tpII/2024-J2-CameraTracker/Diseños 3D/STLs/v7/base v21.stl

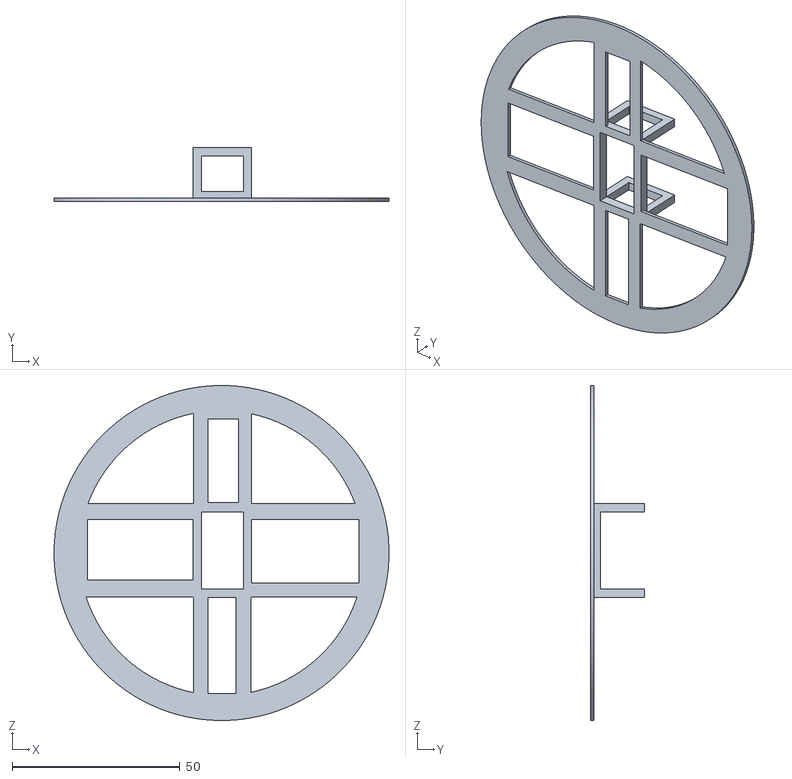
[picture p21: CAD file, 2024-12-09, an earlier design]
Diseños 3D/STLs/v7/base v21.stl
100.0 x 16.0 x 100.0
