tpII/2024-J2-CameraTracker/Diseños 3D/STLs/v2/Servo 2 v16.stl

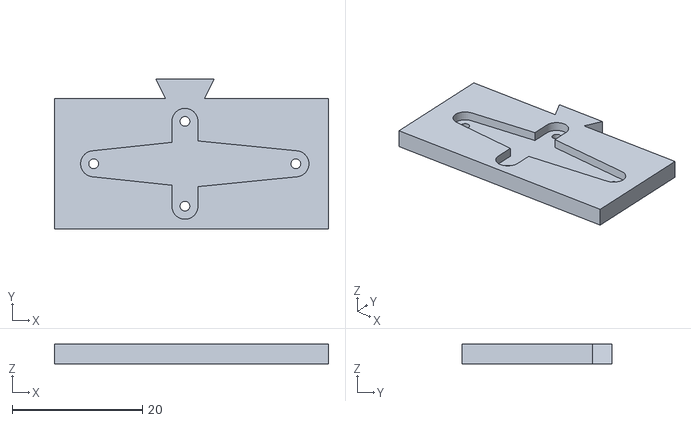
[picture p22: CAD file, 2024-10-07, an earlier design]
Diseños 3D/STLs/v2/Servo 2 v16.stl
42.0 x 23.0 x 3.00
