tpII/2024-J2-CameraTracker/CameraWebServer/web_server.h

#include <WiFi.h>
#include "esp_timer.h"
#include "img_converters.h"
#include "Arduino.h"
#include "fb_gfx.h"
#include "soc/soc.h" //disable brownout problems
#include "soc/rtc_cntl_reg.h"  //disable brownout problems
#include "esp_http_server.h"

#define PART_BOUNDARY "123456789000000000000987654321"
